jpskenn/Sandy/assets/README/DSC_7928.jpeg

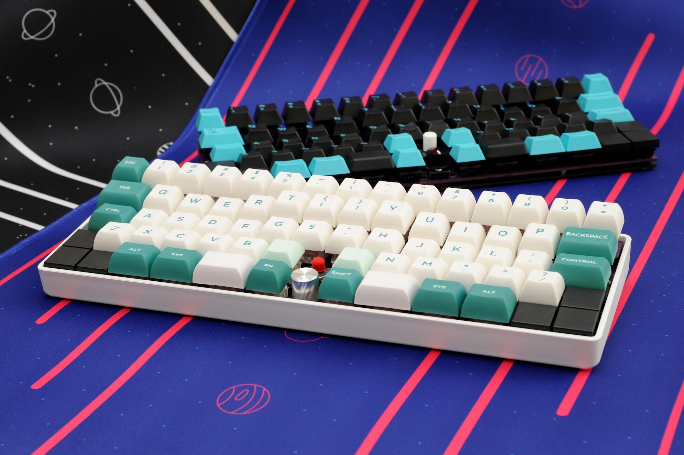
assets/README/DSC_7928.jpeg
