jpskenn/Sandy/Memo/home_position_guide_separate.jpg

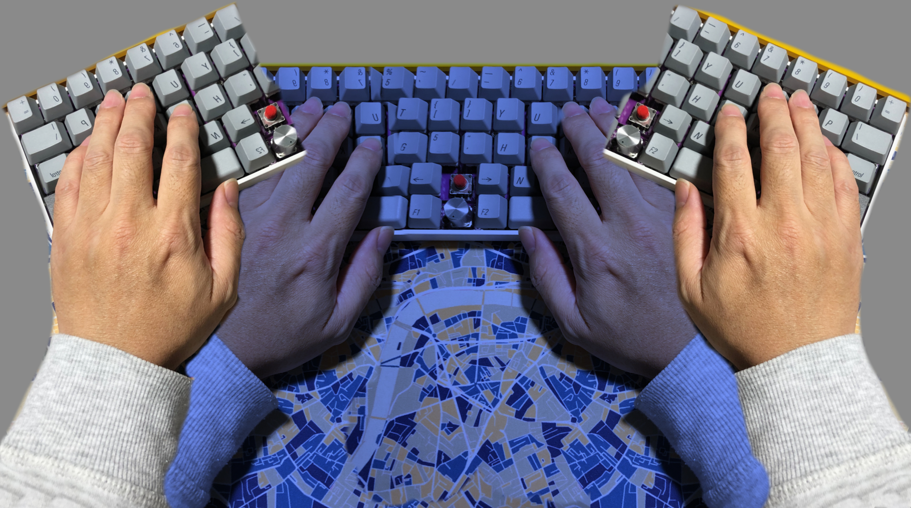
Memo/home_position_guide_separate.jpg
